andycatz/LoRa_Temp_Humidity/Software/PIC18F46K22_LoRa_TEMPHUM_V4.X/defines.h

/* Author: Andy Page
 * Comments: defines.h for MODBUS_TH program
 * Revision history: 1, 26th October 2019
 */

// This is a guard condition so that contents of this file are not included
// more than once.  
#ifndef INC_DEFINES_H
#define	INC_DEFINES_H

#define _XTAL_FREQ 64000000
#define GREEN_LED LATEbits.LATE1 //Green LED output port
#define RED_LED LATEbits.LATE2 //Red LED output port


#endif	/* INC_DEFINES_H */
