andycatz/LoRa_Temp_Humidity/Photos/20210512_200442.jpg

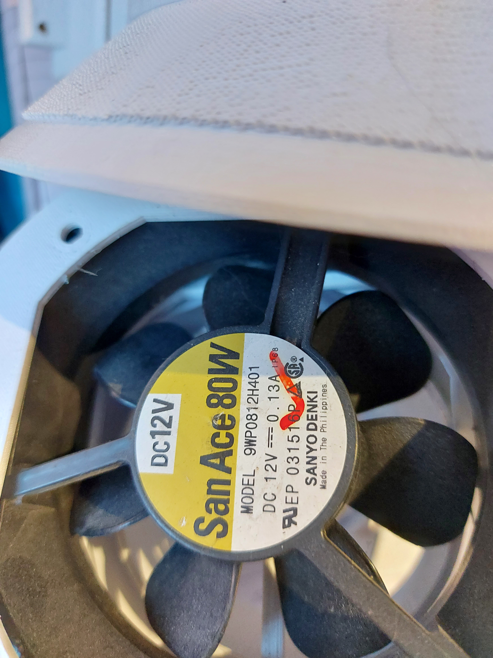
Photos/20210512_200442.jpg
